retasquid/FormulaStudent-Tableau-de-bord/photos/Dimensions_cartes.png

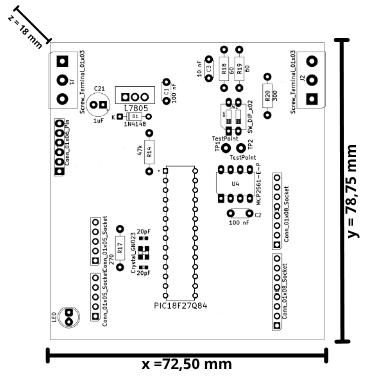
photos/Dimensions_cartes.png
