retasquid/FormulaStudent-Tableau-de-bord/photos/Schema_projet.png

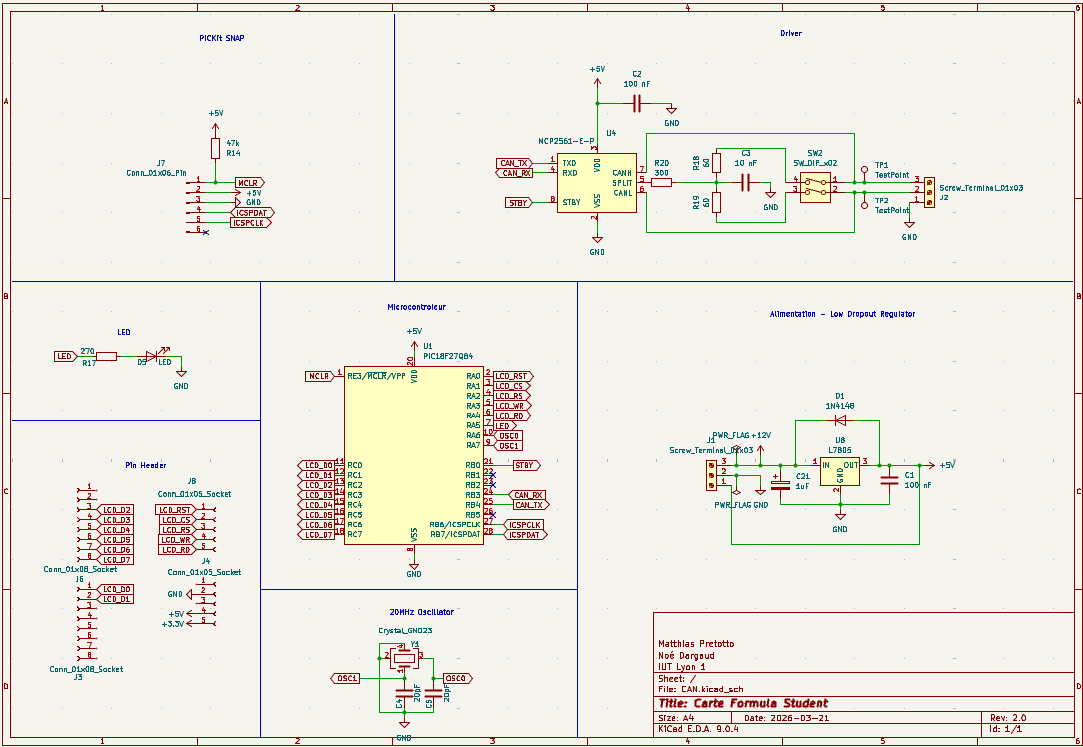
photos/Schema_projet.png
