retasquid/FormulaStudent-Tableau-de-bord/photos/Synoptique.png

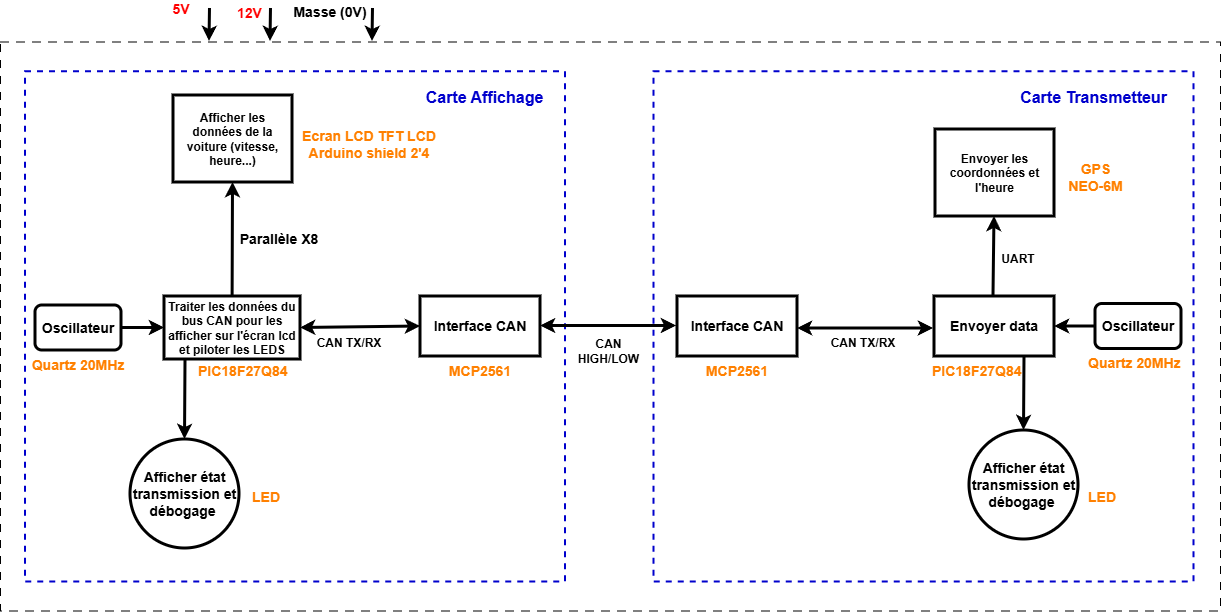
photos/Synoptique.png
