retasquid/FormulaStudent-Tableau-de-bord/codelcd.X/lcd_font.h

#ifndef LCD_FONT_H
#define LCD_FONT_H

#include <stdint.h>

#define LENGHT 10
#define HEIGHT 21

//Police d'ecriture Rubik-Regular 10*21
const uint16_t Font10x21[95][21] = {
    { 0x000, 0x000, 0x000, 0x000, 0x000, 0x000, 0x000, 0x000, 0x000, 0x000, 0x000, 0x000, 0x000, 0x000, 0x000, 0x000, 0x000, 0x000, 0x000, 0x000, 0x000},
    { 0x000, 0x000, 0x000, 0x000, 0x000, 0x020, 0x030, 0x030, 0x030, 0x030, 0x030, 0x030, 0x030, 0x020, 0x000, 0x000, 0x030, 0x000, 0x000, 0x000, 0x000},
    { 0x000, 0x000, 0x000, 0x000, 0x000, 0x078, 0x078, 0x048, 0x048, 0x000, 0x000, 0x000, 0x000, 0x000, 0x000, 0x000, 0x000, 0x000, 0x000, 0x000, 0x000},
    { 0x000, 0x000, 0x000, 0x000, 0x000, 0x000, 0x04C, 0x0CC, 0x3FE, 0x0C8, 0x088, 0x088, 0x3FE, 0x198, 0x190, 0x110, 0x000, 0x000, 0x000, 0x000, 0x000},
    { 0x000, 0x000, 0x020, 0x030, 0x0F8, 0x18C, 0x184, 0x180, 0x0C0, 0x078, 0x01C, 0x004, 0x104, 0x18C, 0x0FC, 0x030, 0x020, 0x000, 0x000, 0x000, 0x000},
    { 0x000, 0x000, 0x000, 0x000, 0x000, 0x1C3, 0x342, 0x364, 0x36C, 0x348, 0x1D0, 0x037, 0x02D, 0x04D, 0x0CD, 0x08D, 0x107, 0x000, 0x000, 0x000, 0x000},
    { 0x000, 0x000, 0x000, 0x000, 0x000, 0x0F0, 0x198, 0x198, 0x198, 0x1B0, 0x0E0, 0x1E2, 0x332, 0x31E, 0x30C, 0x19E, 0x0F3, 0x000, 0x000, 0x000, 0x000},
    { 0x000, 0x000, 0x000, 0x000, 0x000, 0x030, 0x030, 0x020, 0x020, 0x000, 0x000, 0x000, 0x000, 0x000, 0x000, 0x000, 0x000, 0x000, 0x000, 0x000, 0x000},
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
    { 0x000, 0x000, 0x000, 0x000, 0x000, 0x3F8, 0x31C, 0x30C, 0x304, 0x306, 0x306, 0x306, 0x306, 0x304, 0x304, 0x31C, 0x3F8, 0x000, 0x000, 0x000, 0x000},
    { 0x000, 0x000, 0x000, 0x000, 0x000, 0x1FC, 0x180, 0x180, 0x180, 0x180, 0x1FC, 0x180, 0x180, 0x180, 0x180, 0x180, 0x1FC, 0x000, 0x000, 0x000, 0x000},
    { 0x000, 0x000, 0x000, 0x000, 0x000, 0x1FC, 0x180, 0x180, 0x180, 0x180, 0x180, 0x1FC, 0x180, 0x180, 0x180, 0x180, 0x100, 0x000, 0x000, 0x000, 0x000},
    { 0x000, 0x000, 0x000, 0x000, 0x000, 0x0F8, 0x18C, 0x306, 0x300, 0x300, 0x31E, 0x306, 0x306, 0x306, 0x306, 0x19C, 0x0F8, 0x000, 0x000, 0x000, 0x000},
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
};



#endif
